JeremyLakeyJr/altoids-mesh/enclosure/top_lid.scad

// =============================================================================
// Altoids Mesh Enclosure — Top Lid
// =============================================================================
// Overlapping lid that slides over the bottom-case walls — just like a
// real Altoids tin.  Houses the CardKB keyboard and has an OLED display
// window.
//
// Features:  overlapping skirt · embossed label panel · friction-fit
//            bump at front edge · CardKB mounting ledges & retention
//            clips · hinge knuckles (paper-clip pin)
//
// Sealed design: no through-holes in the top plate.  Keyboard and
// display are accessible only when the lid is hinged open (laptop mode).
// =============================================================================

include <parameters.scad>

// =========================================================================
//  Helper Modules
// =========================================================================

// Rounded rectangle (origin at corner, Z-up)
module rrect(size, r) {
    hull() {
        for (dx = [r, size[0] - r], dy = [r, size[1] - r])
            translate([dx, dy, 0])
                cylinder(r = r, h = size[2], $fn = 36);
    }
}

// CardKB retention clip
module cardkb_clip(len) {
    ch  = 3.0;   // clip height
    ct  = 1.0;   // clip thickness
    coh = 1.2;   // overhang
    cube([len, ct, ch]);
    translate([-coh, 0, ch - ct])
        cube([len + coh * 2, ct, ct]);
}

// ----- Lid Hinge Knuckle (lid side) ------------------------------------------
// In lid-local coordinates the hinge axis is at Y = 0, Z = lid_ext_depth
// (maps to the back-edge hinge axis when the lid is flipped in assembly).
module lid_hinge_knuckle(x_pos, klen) {
    barrel_r = hinge_barrel_d / 2;
    translate([x_pos, 0, lid_ext_depth]) {
        difference() {
            union() {
                rotate([0, 90, 0])
                    cylinder(d = hinge_barrel_d, h = klen, $fn = 24);
                // Arm toward lid body (+Y)
                translate([0, 0, -barrel_r])
                    cube([klen, hinge_arm_t, barrel_r]);
            }
            // Pin hole (paper-clip clearance)
            translate([-0.1, 0, 0])
                rotate([0, 90, 0])
                    cylinder(d = hinge_pin_d + tolerance * 2,
                             h = klen + 0.2, $fn = 24);
        }
    }
}

// =========================================================================
//  Main Top Lid
// =========================================================================
module top_lid() {
    // Offsets caused by the wider lid vs case
    lid_off = lid_wall + snap_clearance;   // extra width per side

    difference() {
        union() {
            // ----------------------------------------------------------
            //  Outer shell  (top plate + skirt walls)
            // ----------------------------------------------------------
            // Top plate at full lid footprint
            rrect([lid_ext_len, lid_ext_wid, lid_top_t],
                  corner_r + lid_off);

            // Skirt (short walls that slide over the case)
            difference() {
                rrect([lid_ext_len, lid_ext_wid, lid_top_t + lid_overlap],
                      corner_r + lid_off);
                // Hollow out the interior of the skirt
                translate([lid_wall, lid_wall, -0.1])
                    rrect([lid_ext_len - lid_wall * 2,
                           lid_ext_wid - lid_wall * 2,
                           lid_top_t + lid_overlap + 0.2],
                          corner_r + lid_off - lid_wall);
            }

            // Interior pocket walls (for CardKB recess depth)
            // Pocket must fit inside the case walls with clearance
            translate([lid_off + wall + snap_clearance,
                       lid_off + wall + snap_clearance, lid_top_t])
                difference() {
                    rrect([int_len - snap_clearance * 2,
                           int_wid - snap_clearance * 2,
                           lid_int_depth],
                          max(0.5, corner_r - wall));
                    translate([lid_wall, lid_wall, -0.1])
                        rrect([int_len - snap_clearance * 2 - lid_wall * 2,
                               int_wid - snap_clearance * 2 - lid_wall * 2,
                               lid_int_depth + 0.2],
                              max(0.5, corner_r - wall - lid_wall));
                }

            // ----------------------------------------------------------
            //  Friction-fit bump on front skirt (Altoids-style catch)
            // ----------------------------------------------------------
            translate([lid_ext_len / 2 - friction_bump_w / 2,
                       0,
                       lid_top_t + lid_overlap * 0.4])
                cube([friction_bump_w, lid_wall + friction_bump_h,
                      lid_overlap * 0.3]);

            // ----------------------------------------------------------
            //  CardKB support ledges  (1 mm clearance all around)
            // ----------------------------------------------------------
            kb_ledge_h = lid_int_depth - cardkb_ht;

            // Left ledge
            translate([lid_off + wall + cardkb_pos_x - 1.0,
                       lid_off + wall + cardkb_pos_y - 1.0,
                       lid_top_t])
                cube([cardkb_len + 2, 1.5, kb_ledge_h]);

            // Right ledge
            translate([lid_off + wall + cardkb_pos_x - 1.0,
                       lid_off + wall + cardkb_pos_y + cardkb_wid - 0.5,
                       lid_top_t])
                cube([cardkb_len + 2, 1.5, kb_ledge_h]);

            // Front ledge
            translate([lid_off + wall + cardkb_pos_x - 1.0,
                       lid_off + wall + cardkb_pos_y - 1.0,
                       lid_top_t])
                cube([1.5, cardkb_wid + 2, kb_ledge_h]);

            // Back ledge
            translate([lid_off + wall + cardkb_pos_x + cardkb_len - 0.5,
                       lid_off + wall + cardkb_pos_y - 1.0,
                       lid_top_t])
                cube([1.5, cardkb_wid + 2, kb_ledge_h]);

            // ----------------------------------------------------------
            //  CardKB retention clips (four corners)
            // ----------------------------------------------------------
            for (cx = [5, cardkb_len - 15])
                for (cy = [-0.5, cardkb_wid - 0.5])
                    translate([lid_off + wall + cardkb_pos_x + cx,
                               lid_off + wall + cardkb_pos_y + cy,
                               lid_top_t + kb_ledge_h])
                        cardkb_clip(10);

            // ----------------------------------------------------------
            //  Hinge knuckles  (lid gets knuckles 1, 3)
            // ----------------------------------------------------------
            // Shift by lid_off so knuckles align with case knuckles.
            // Y = lid_off maps to Y = case_ext_wid after assembly
            // (the 180° flip inverts Y).
            translate([lid_off, lid_off, 0])
            for (i = [1, 3]) {
                xp = hinge_margin + i * (hinge_knuckle_l + hinge_gap);
                barrel_r = hinge_barrel_d / 2;
                translate([xp, 0, lid_top_t + lid_overlap]) {
                    difference() {
                        union() {
                            rotate([0, 90, 0])
                                cylinder(d = hinge_barrel_d,
                                         h = hinge_knuckle_l, $fn = 24);
                            // Arm toward lid body (+Y local = toward
                            // case interior after 180° assembly flip)
                            translate([0, 0, -barrel_r])
                                cube([hinge_knuckle_l, hinge_arm_t,
                                      barrel_r]);
                        }
                        translate([-0.1, 0, 0])
                            rotate([0, 90, 0])
                                cylinder(d = hinge_pin_d + tolerance * 2,
                                         h = hinge_knuckle_l + 0.2,
                                         $fn = 24);
                    }
                }
            }
        }

        // ==============================================================
        //  Subtractive features
        // ==============================================================

        // NOTE: keyboard and display openings removed for sealed design.
        // Keys and OLED are accessible through the open lid pocket in
        // laptop mode; no through-holes in the top plate when closed.

        // CardKB cable routing slot
        translate([lid_off + wall + cardkb_pos_x
                       + cardkb_cable_off - cardkb_cable_w / 2 - 1,
                   lid_off + wall + cardkb_pos_y - 1,
                   lid_top_t])
            cube([cardkb_cable_w + 2, wall + 2, cardkb_ht + 2]);

        // Embossed label panel (shallow recess on lid top)
        translate([emboss_inset, emboss_inset, -0.1])
            rrect([lid_ext_len - emboss_inset * 2,
                   lid_ext_wid - emboss_inset * 2,
                   emboss_depth + 0.1],
                  emboss_r);

        // NOTE: corner screw holes removed for sealed design.
        // Lid closure relies on friction-fit bump + hinge.
    }
}

// Render when opened directly
top_lid();
